McOrts/domohome/images/IMG_2598.JPG

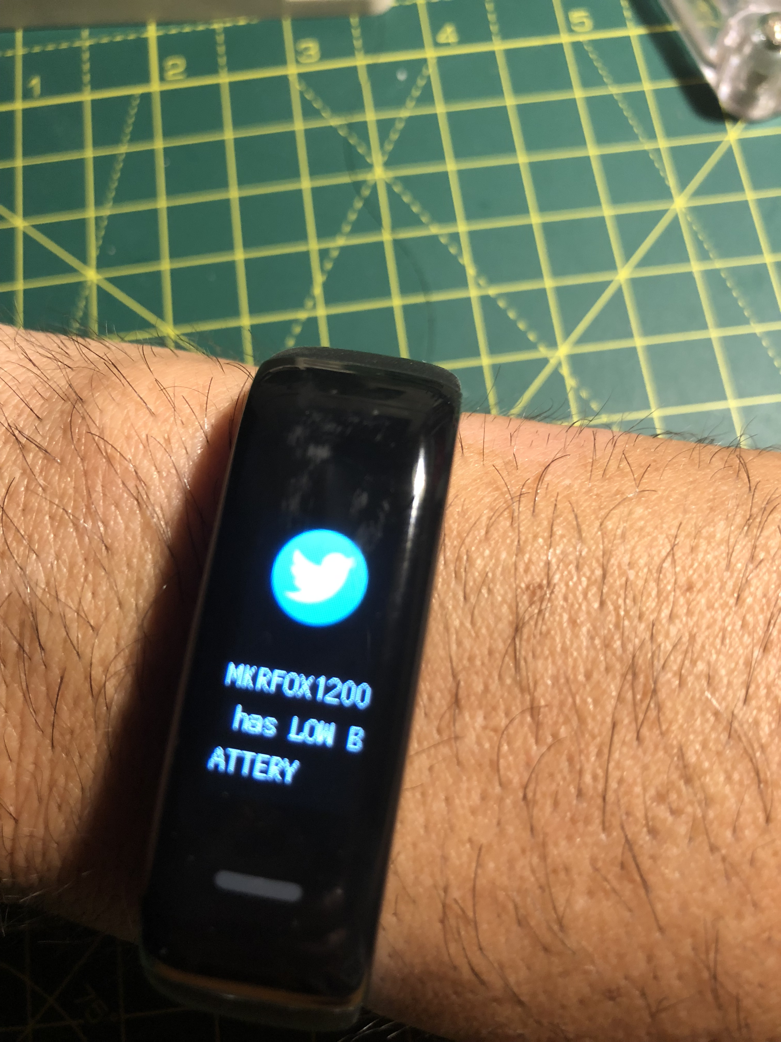
images/IMG_2598.JPG
